Barsy-Barsevich/AH3-hardware/Documentation/AH3_Init_algorithm.jpg

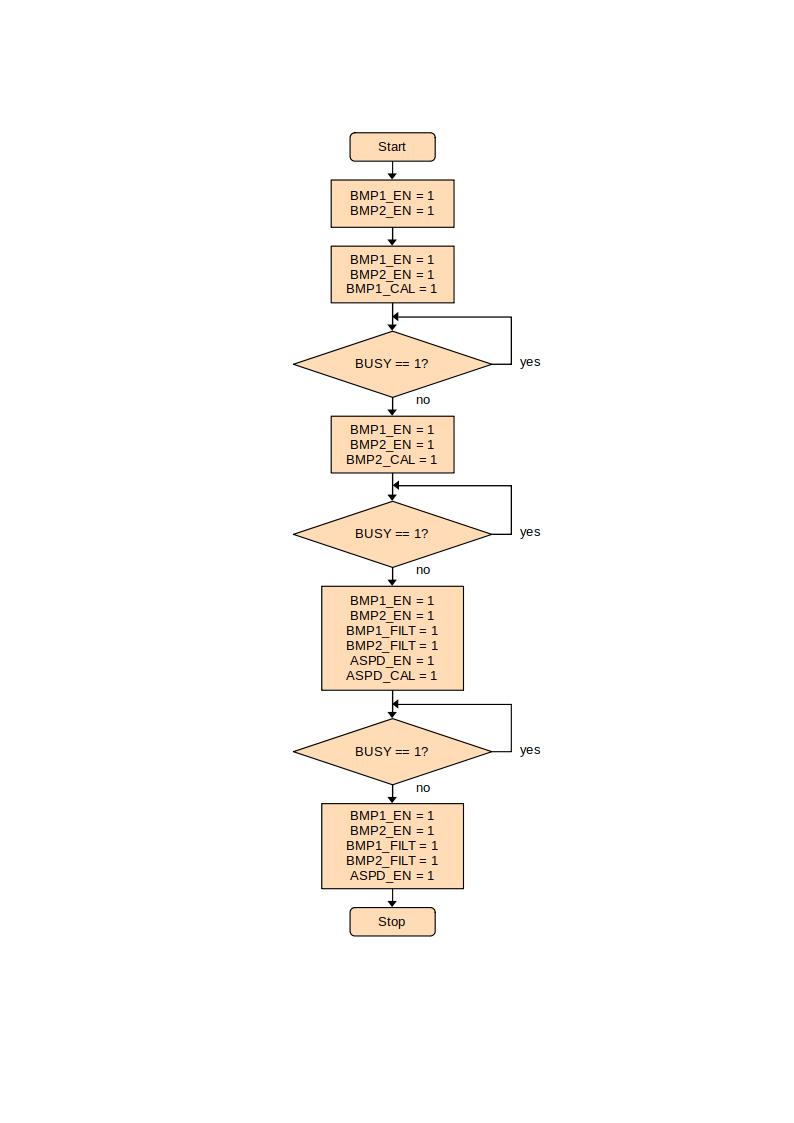
Documentation/AH3_Init_algorithm.jpg
