Barsy-Barsevich/AH3-hardware/Photoes/photo_2024-11-07_13-37-18 (2).jpg

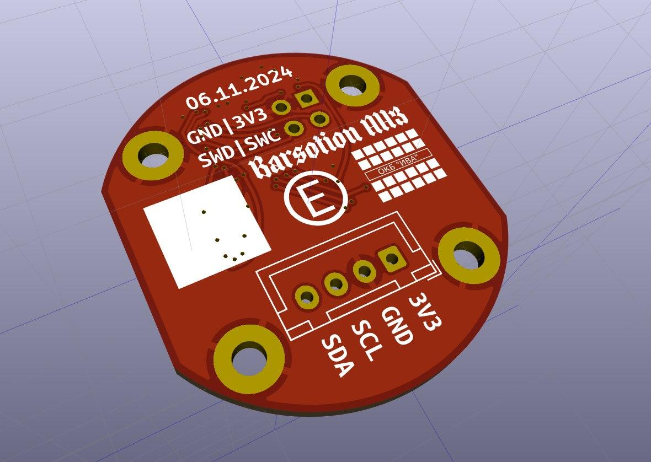
Photoes/photo_2024-11-07_13-37-18 (2).jpg
