Barsy-Barsevich/AH3-hardware/Photoes/photo_2024-11-25_15-48-12.jpg

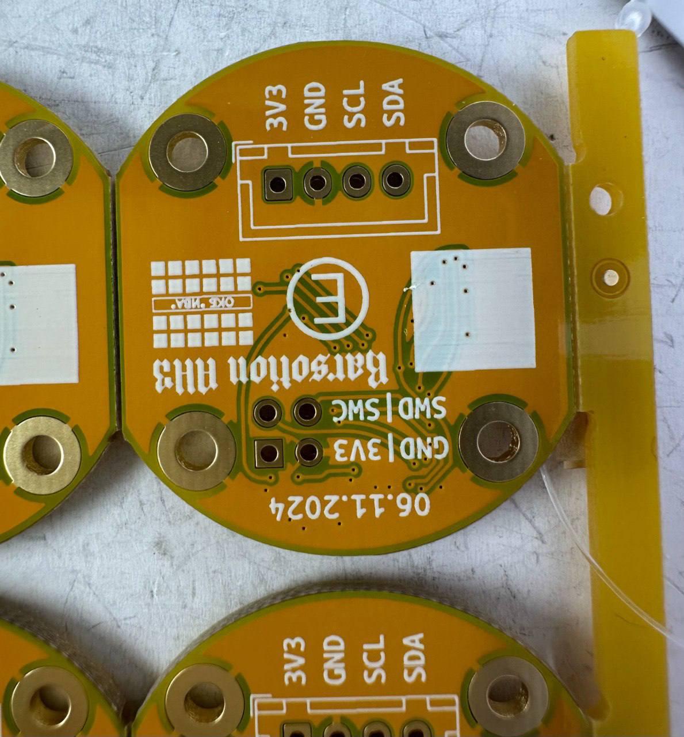
Photoes/photo_2024-11-25_15-48-12.jpg
