Barsy-Barsevich/AH3-hardware/Photoes/photo_2025-01-24_00-12-46.jpg

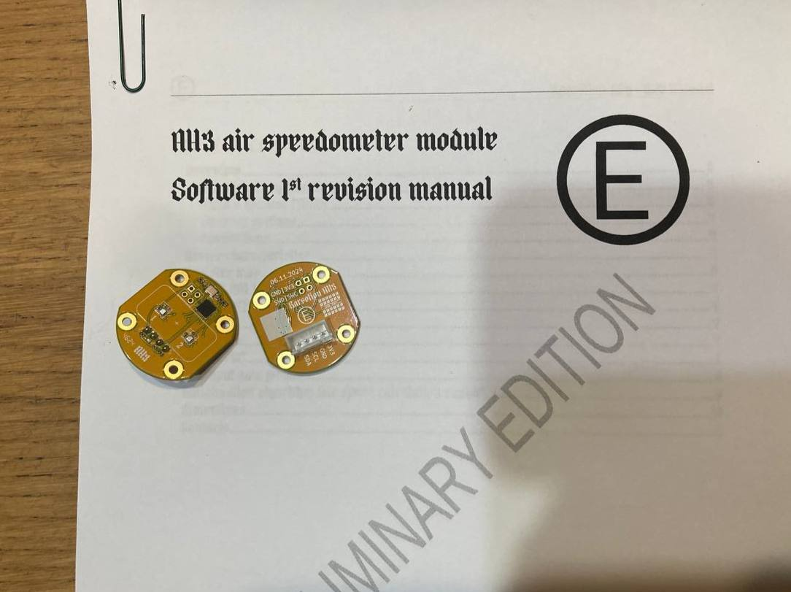
Photoes/photo_2025-01-24_00-12-46.jpg
